sheelis/cnc-spindle-light/photos/IMG_20201206_210829.jpg

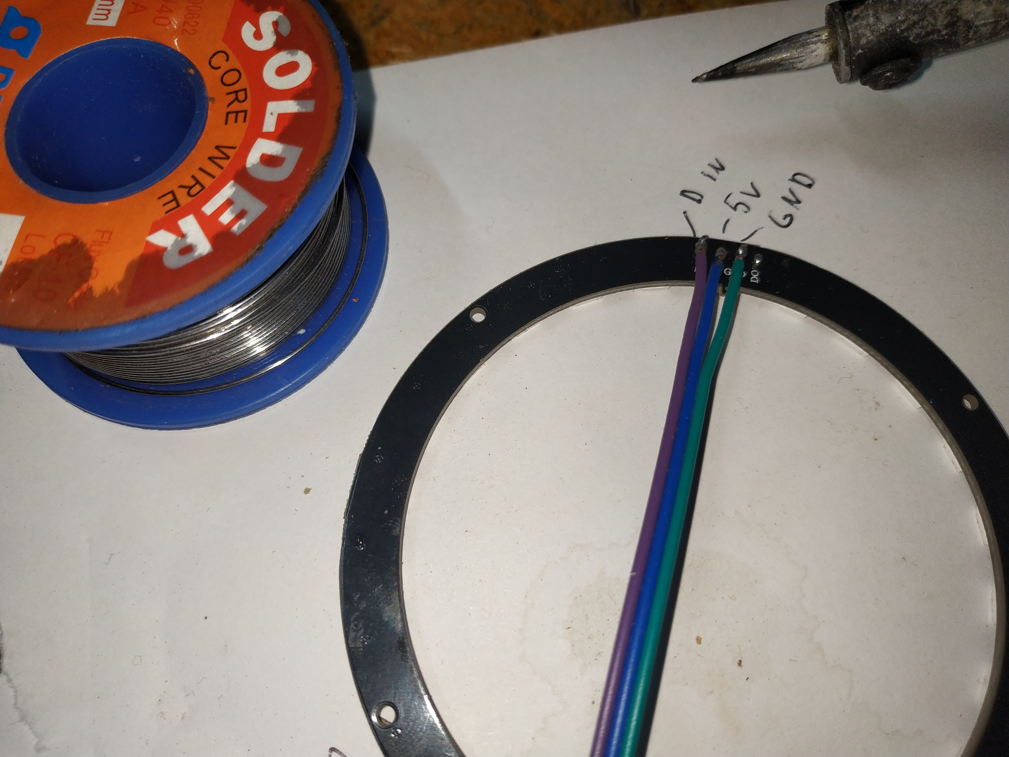
photos/IMG_20201206_210829.jpg
