sheelis/cnc-spindle-light/photos/IMG_20201206_211432.jpg

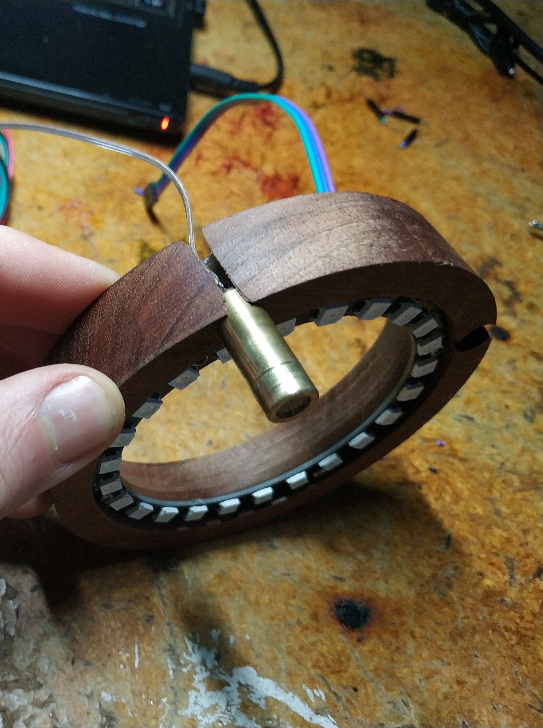
photos/IMG_20201206_211432.jpg
